Rodrigo-Brasileiro/gs-maker-lab/imagens/barra.png

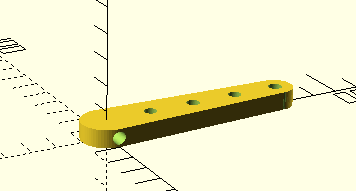
imagens/barra.png
