Rodrigo-Brasileiro/gs-maker-lab/imagens/vista_de_cima.png

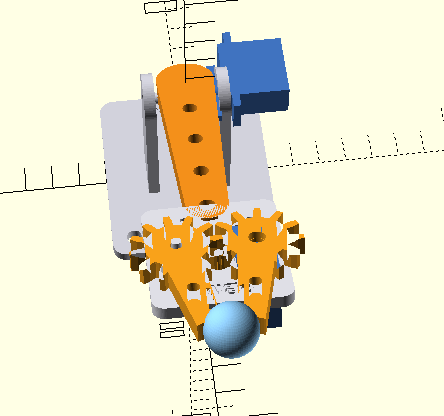
imagens/vista_de_cima.png
